SadaleNet/ilo-musi-8/label/ima_brandlabel_50x25mm.png

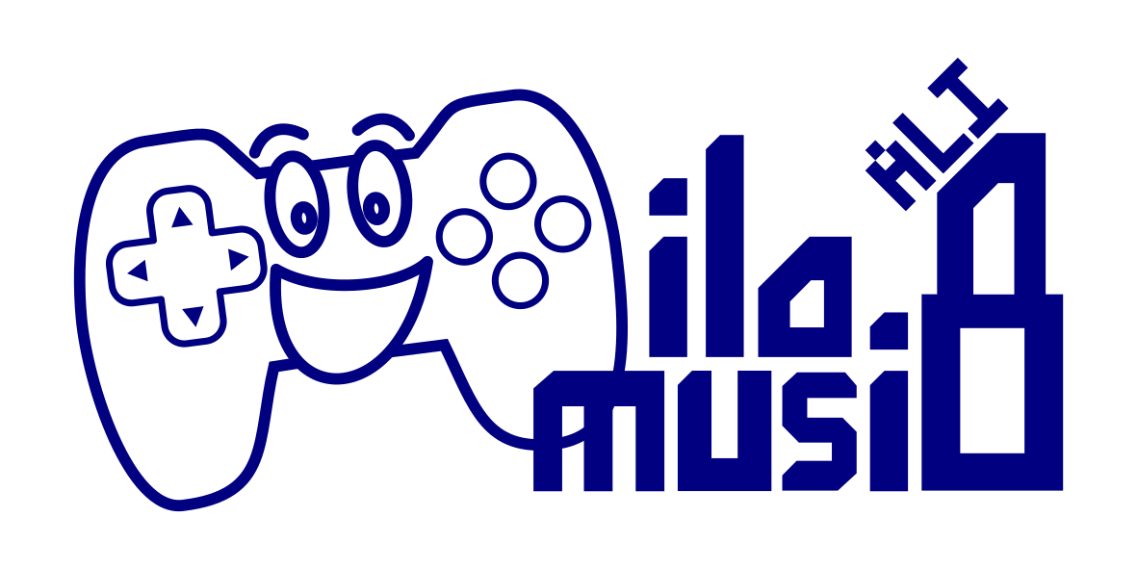
label/ima_brandlabel_50x25mm.png
