SadaleNet/ilo-musi-8/label/ima_cardboard_label_a4.png

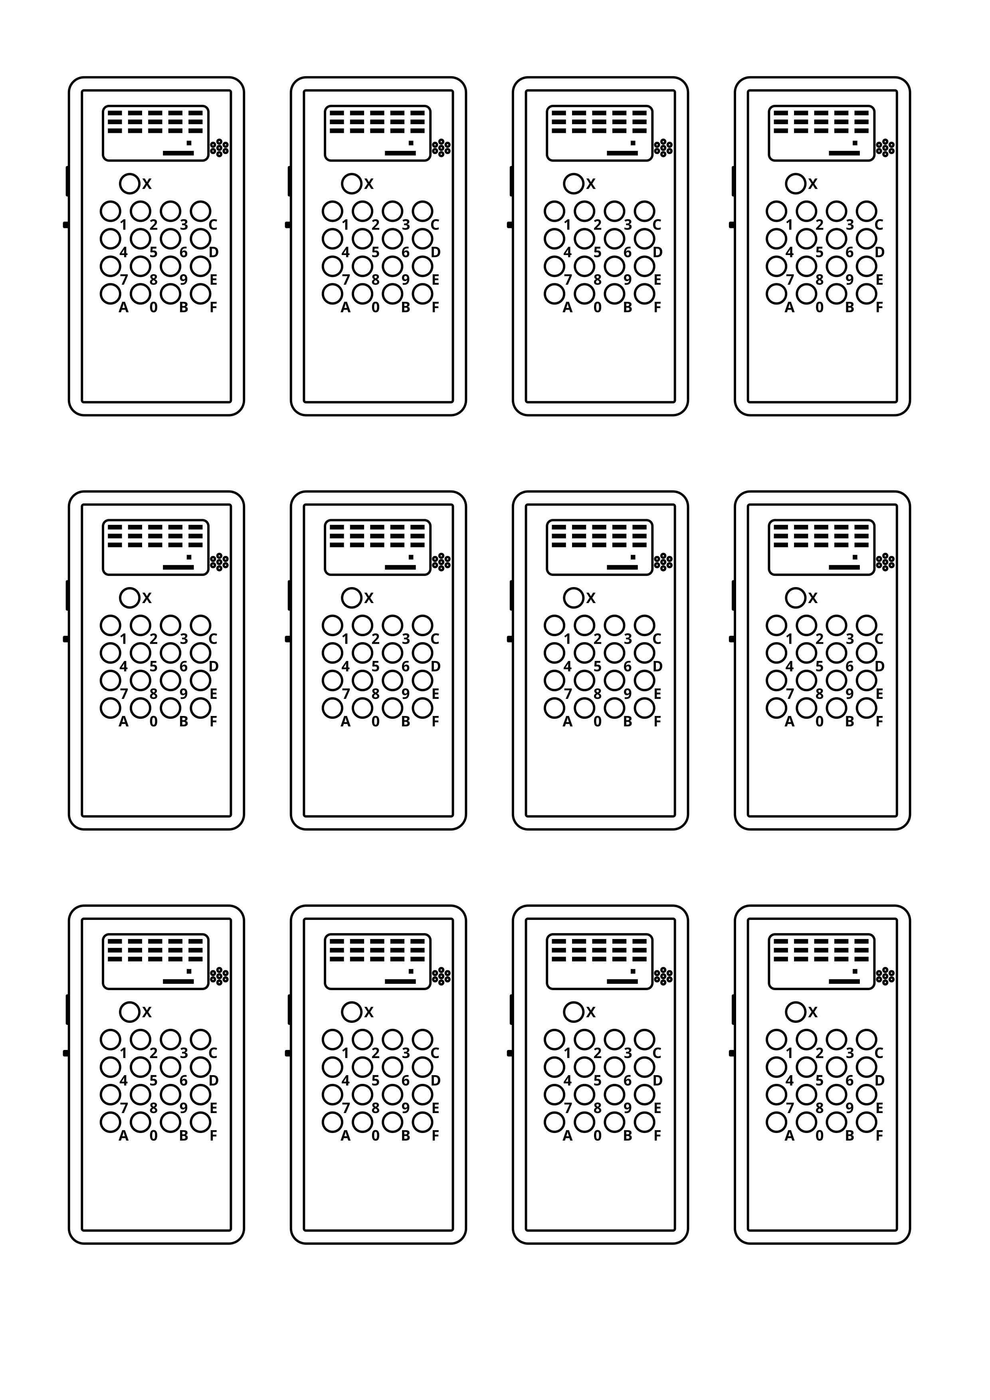
label/ima_cardboard_label_a4.png
