SadaleNet/ilo-musi-8/label/ima_keylabel_46.1x54.4mm.png

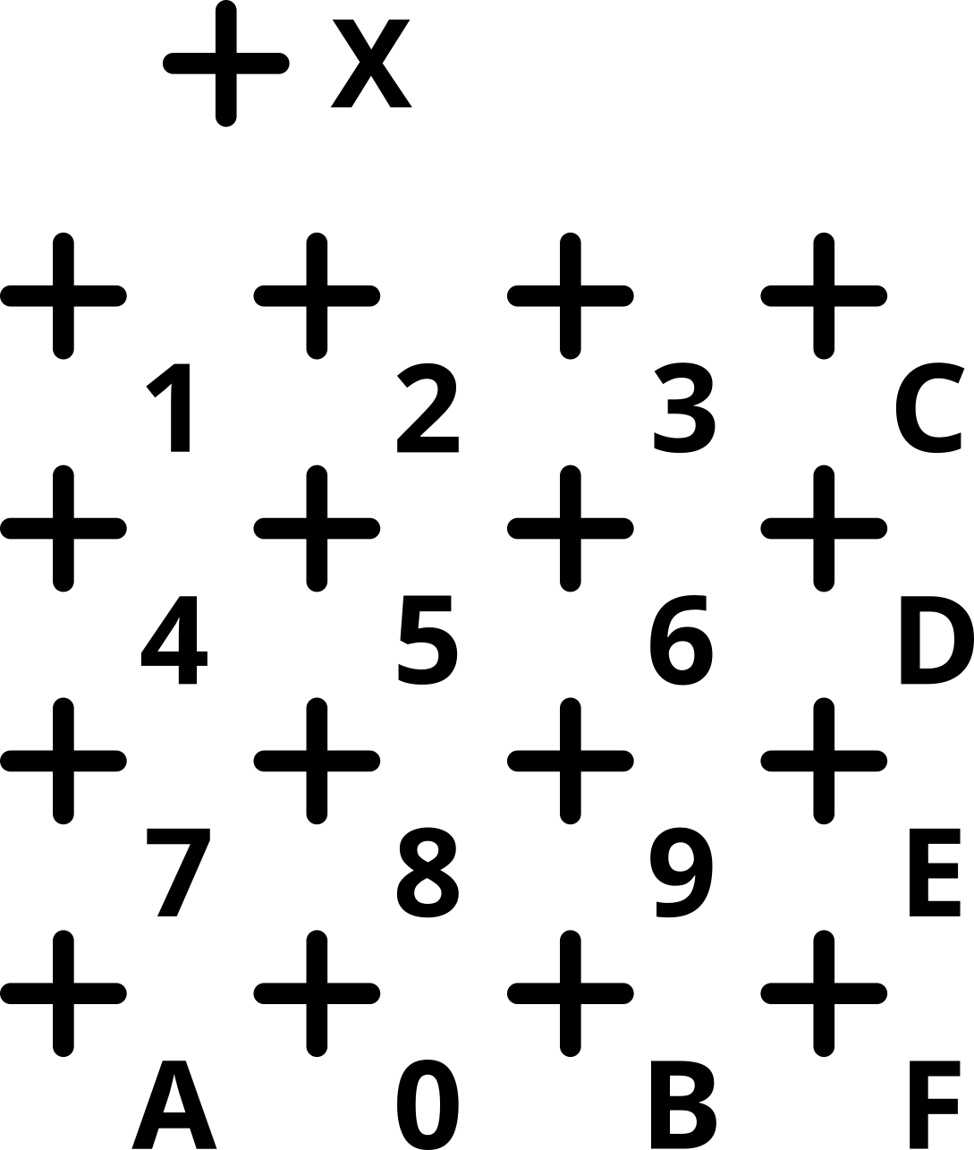
label/ima_keylabel_46.1x54.4mm.png
