SadaleNet/ilo-musi-8/firmware/spi.c

// Copyright 2026 Wong Cho Ching <https://sadale.net>
//
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
// 1. Redistributions of source code must retain the above copyright
// notice, this list of conditions and the following disclaimer.
//
// 2. Redistributions in binary form must reproduce the above copyright
// notice, this list of conditions and the following disclaimer in the
// documentation and/or other materials provided with the distribution.
//
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
#include "adc.h"
#include "lcd.h"
#include "spi.h"

#include "ch32fun.h"

void spi_init(void) {
	// This module owns the following pins: CARD_CS, SCK, MOSI, MISO
	// Keep in mind that, in particular, LCD_CS is owned by the lcd module, and that
	// the SPI DMA isn't being owned by this module because only LCD uses it.

	// Enable the GPIO
	RCC->PB2PCENR |= RCC_IOPCEN;

	// Reset SPI
	RCC->PB2PRSTR |= RCC_SPI1RST;
	RCC->PB2PRSTR &= ~RCC_SPI1RST;
	// Enable the SPI clock source
	RCC->PB2PCENR |= RCC_SPI1EN;

	// Reset SPI
	RCC->PB2PRSTR |= RCC_SPI1RST;
	RCC->PB2PRSTR &= ~RCC_SPI1RST;
	// Enable the SPI clock source
	RCC->PB2PCENR |= RCC_SPI1EN;

	// Configure SPI. SPI_Mode_Master and SPI_CTLR1_SPE must be set after CS pin is high
	SPI1->CTLR1 =	SPI_CTLR1_BR_2 | SPI_CTLR1_BR_1 | SPI_CTLR1_BR_0 // Same as lcd_spi_set_mode(SPI_MODE_MEMORY_CARD_SLOW)
					| (SPI_CPOL_Low | SPI_CPHA_1Edge) // SPI Mode 0 (That's for the card. LCD requires SPI mode 3 instead (SPI_CPOL_High | SPI_CPHA_2Edge))
					| SPI_NSS_Soft // Software NSS mode
					| SPI_Mode_Master // Master mode
					| 0 // (lack of SPI_CTLR1_DFF) 8bit mode
					| SPI_Direction_2Lines_FullDuplex // Use both MOSI and MISO
					| SPI_CTLR1_SPE; // SPI begin!

	// Enable DMA (other component may also enable DMA on their own. No harm to enable it multiple times.)
	RCC->HBPCENR |= RCC_DMA1EN;

	// Configure DMA for SPI TX
	DMA1_Channel3->PADDR = (uint32_t)(&SPI1->DATAR); // Peripheral address register

	DMA1_Channel3->CFGR =
		// (Not specifying DMA_CFGR1_PL) Set the priority to "Low"
		// (Not specifying DMA_CFGR1_PSIZE) 8bit data for peripheral
		// (Not specifying DMA_CFGR1_MSIZE) 8bit data for memory
		DMA_CFGR1_MINC | // Incrememt memory address
		DMA_CFGR1_DIR | // Read from memory, write to peripheral
		DMA_CFGR1_TCIE; // Enable transfer-complete interrupt

	// Configure interrupt controller
	DMA1->INTFCR |= DMA_CTCIF3; // Clear the transfer-complete interrupt flag for SPI TX, just in case.
	PFIC->IPRIOR[DMA1_Channel3_IRQn] = 0x80; // The priority is 0x80 (the highest but that it can be preempted)

	// Configure DMA for SPI RX
	DMA1_Channel2->PADDR = (uint32_t)(&SPI1->DATAR); // Peripheral address register
	DMA1_Channel2->CFGR =
		(DMA_CFGR1_PL_1|DMA_CFGR1_PL_0) | // Set the priority to "Very High"
		// (Not specifying DMA_CFGR1_PSIZE) 8bit data for peripheral
		// (Not specifying DMA_CFGR1_MSIZE) 8bit data for memory
		DMA_CFGR1_MINC; // Incrememt memory address
		// (Not spedifying DMA_CFGR1_DIR) Read from peripheral, write to memory


	// Card CS pin is P0
	// SPI pins are PC5 SCK, PC6 MOSI, and PC7 MISO
	GPIOC->CFGLR &= ~((GPIO_CFGLR_MASK << (4*0)) | (GPIO_CFGLR_MASK << (4*5)) | (GPIO_CFGLR_MASK << (4*6)) | (GPIO_CFGLR_MASK << (4*7)));
	GPIOC->CFGLR |= (GPIO_CFGLR_OUT_PP << (4*0)) | (GPIO_CFGLR_OUT_AF_PP << (4*5)) | (GPIO_CFGLR_OUT_AF_PP << (4*6)) | (GPIO_CFGLR_IN_FLOAT << (4*7));

	spi_set_mode(SPI_MODE_MEMORY_CARD_SLOW);
}

void spi_send_byte(uint8_t data) {
	while(!(SPI1->STATR & SPI_STATR_TXE)){}
	SPI1->DATAR = data;
	// Wait until completion of transfer.
	// That's because we might want to change the slave select line
	// or other control lines right after calling this function.
	while(SPI1->STATR & SPI_STATR_BSY){}
}

void spi_set_mode(enum spi_mode mode) {
	// Always wait until LCD transfer completion
	// even if we're switching to SPI_MODE_LCD.
	// That's because a switch from SPI_MODE_LCD to SPI_MODE_LCD
	// would still cause disruption to the SPI bus
	while(lcd_is_transfer_in_progress()){}

	switch(mode) {
		case SPI_MODE_LCD:
			lcd_set_backlight_suppression(false);
			// Go back to LCD mode (mode 3)
			//SPI1->CTLR1 &= ~(SPI_CPOL_High | SPI_CPHA_2Edge); // redundant because we're gonna use |=
			SPI1->CTLR1 |= (SPI_CPOL_High | SPI_CPHA_2Edge);

			// LCD max 20Mhz
			// Setting the divider to 4. That'd be 48Mhz/4 = 12Mhz.
			SPI1->CTLR1 &= ~SPI_CTLR1_BR;
			SPI1->CTLR1 |= SPI_CTLR1_BR_0;

			// PFIC: Enable interrupt for DMA1_Channel3_IRQn (SPI TX, used by LCD)
			DMA1->INTFCR |= DMA_CTCIF3; // Clear the transfer-complete interrupt flag so that the interrupt handler won't get misfired right away
			DMA1_Channel3->CFGR |= DMA_CFGR1_TCIE;
			PFIC->IENR[DMA1_Channel3_IRQn/32] |= (1<<(DMA1_Channel3_IRQn%32));
		break;
		case SPI_MODE_MEMORY_CARD:
		case SPI_MODE_MEMORY_CARD_SLOW:
			lcd_set_backlight_suppression(true);
			SPI1->DATAR; // Clear the RX byte

			// PFIC: Disable interrupt for DMA1_Channel3_IRQn (SPI TX, used by LCD)
			PFIC->IRER[DMA1_Channel3_IRQn/32] |= (1<<(DMA1_Channel3_IRQn%32));
			DMA1_Channel3->CFGR &= ~DMA_CFGR1_TCIE;

			// Switch to SPI mode 0 for memory card
			SPI1->CTLR1 &= ~(SPI_CPOL_High | SPI_CPHA_2Edge);

			if(mode == SPI_MODE_MEMORY_CARD) {
				// Card max 25Mhz
				// Setting the divider to 2. That'd be 48Mhz/2 = 24Mhz
				SPI1->CTLR1 &= ~SPI_CTLR1_BR;
			} else { // mode == SPI_MODE_MEMORY_CARD_SLOW
				// Required data rate for card: 100kHz ~ 400kHz
				// Setting the divider to 256. That'd be 48Mhz/256 = 187kHz
				// SPI1->CTLR1 &= ~SPI_CTLR1_BR; // Commenting out. Redundant.
				SPI1->CTLR1 |= SPI_CTLR1_BR_2 | SPI_CTLR1_BR_1 | SPI_CTLR1_BR_0;
			}
		break;
	}
}
